KolijnWolfaardt/TTN_sensor_node/Firmware/inc/config_bits.h

/* 
 * File:   hardware_config.h
 * Author: kolijn
 *
 * Created on 11 April 2017, 6:55 AM
 */

#ifndef HARDWARE_CONFIG_H
#define	HARDWARE_CONFIG_H

#define OSC_FREQ 16000000

#include <xc.h>

// #pragma config statements should precede project file includes.
// Use project enums instead of #define for ON and OFF.

// CONFIG1L
#pragma config WDTEN = OFF      // Watchdog Timer (Disabled - Controlled by SWDTEN bit)
#pragma config PLLDIV = 4       // PLL Prescaler Selection bits (Divide by 4 (16 MHz oscillator input))
#pragma config STVREN = ON      // Stack Overflow/Underflow Reset  (Enabled)
#pragma config XINST = OFF      // Extended Instruction Set (Disabled)

// CONFIG1H
#pragma config CPUDIV = OSC1    // CPU System Clock Postscaler (No CPU system clock divide)
#pragma config CP0 = OFF        // Code Protect (Program memory is not code-protected)

// CONFIG2L
#pragma config OSC = HSPLL      // Oscillator (HS+PLL, USB-HS+PLL)
#pragma config T1DIG = ON       // T1OSCEN Enforcement (Secondary Oscillator clock source may be selected)
#pragma config LPT1OSC = OFF    // Low-Power Timer1 Oscillator (High-power operation)
#pragma config FCMEN = ON       // Fail-Safe Clock Monitor (Enabled)
#pragma config IESO = ON        // Internal External Oscillator Switch Over Mode (Enabled)

// CONFIG2H
#pragma config WDTPS = 32768    // Watchdog Postscaler (1:32768)

// CONFIG3L
#pragma config DSWDTOSC = INTOSCREF// DSWDT Clock Select (DSWDT uses INTRC)
#pragma config RTCOSC = INTOSCREF// RTCC Clock Select (RTCC uses T1OSC/T1CKI)
#pragma config DSBOREN = ON     // Deep Sleep BOR (Enabled)
#pragma config DSWDTEN = ON     // Deep Sleep Watchdog Timer (Enabled)
#pragma config DSWDTPS = G2     // Deep Sleep Watchdog Postscaler (1:2,147,483,648 (25.7 days))

// CONFIG3H
#pragma config IOL1WAY = ON     // IOLOCK One-Way Set Enable bit (The IOLOCK bit (PPSCON<0>) can be set once)
#pragma config MSSP7B_EN = MSK7 // MSSP address masking (7 Bit address masking mode)

// CONFIG4L
#pragma config WPFP = PAGE_63   // Write/Erase Protect Page Start/End Location (Write Protect Program Flash Page 63)
#pragma config WPEND = PAGE_WPFP// Write/Erase Protect Region Select (valid when WPDIS = 0) (Page WPFP<5:0> through Configuration Words erase/write protected)
#pragma config WPCFG = OFF      // Write/Erase Protect Configuration Region (Configuration Words page not erase/write-protected)

// CONFIG4H
#pragma config WPDIS = OFF      // Write Protect Disable bit (WPFP<5:0>/WPEND region ignored)


#endif	/* HARDWARE_CONFIG_H */
